lnxrobots/rcj-soccer-open/Hardware/3D/handle/handle-mount.stl

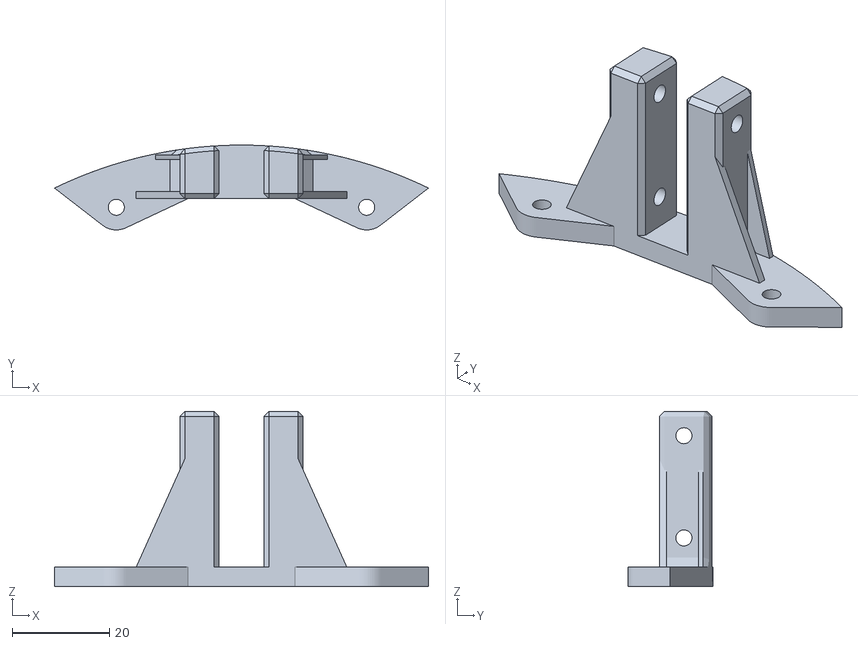
[picture p15: CAD file, 2023-08-07]
Hardware/3D/handle/handle-mount.stl
76.9 x 17.4 x 36.0
