lnxrobots/rcj-soccer-open/Hardware/3D/rack.stl

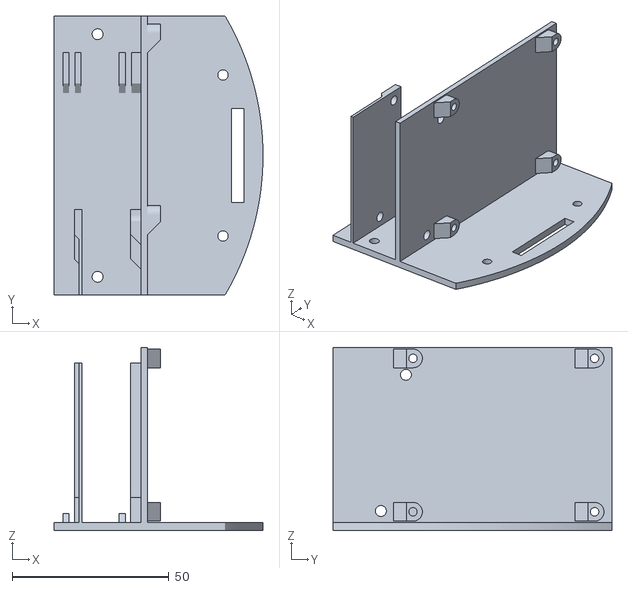
[picture p16: CAD file, 2023-08-07]
Hardware/3D/rack.stl
66.8 x 89.0 x 58.5
