lnxrobots/rcj-soccer-open/Hardware/3D/transport-container-adapter/adapter.stl

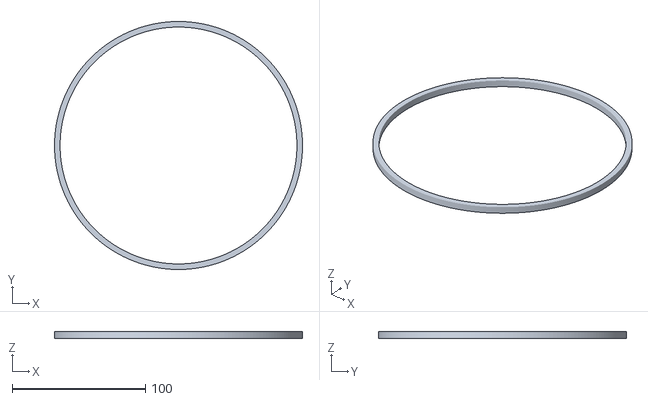
[picture p17: CAD file, 2023-08-07]
Hardware/3D/transport-container-adapter/adapter.stl
186.0 x 186.0 x 5.00
