lnxrobots/rcj-soccer-open/Hardware/3D/bumpers-35mm/bumper-side.stl

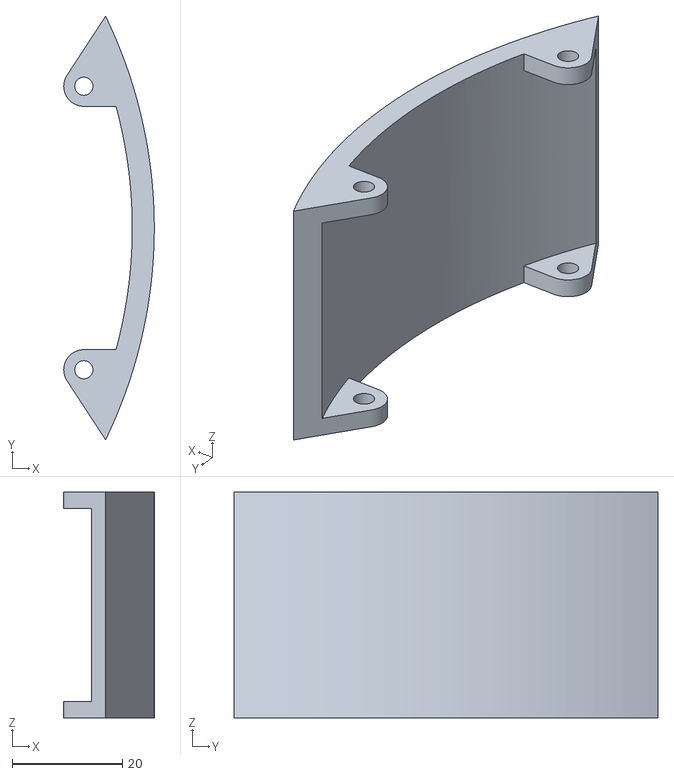
[picture p19: CAD file, 2023-08-07]
Hardware/3D/bumpers-35mm/bumper-side.stl
16.4 x 76.9 x 41.0
