lnxrobots/rcj-soccer-open/Hardware/3D/bumpers-40mm/bumper-40mm-front.stl

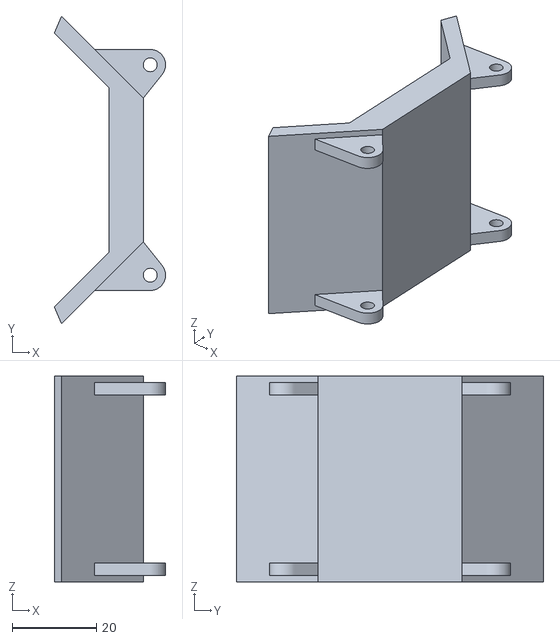
[picture p20: CAD file, 2023-08-07]
Hardware/3D/bumpers-40mm/bumper-40mm-front.stl
26.4 x 73.1 x 49.0
