lnxrobots/rcj-soccer-open/Hardware/3D/pcb-shaft.stl

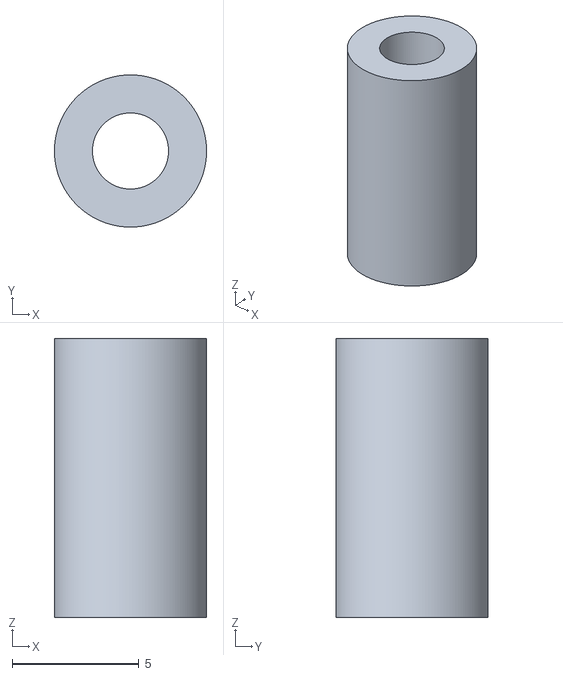
[picture p21: CAD file, 2023-08-07]
Hardware/3D/pcb-shaft.stl
6.00 x 6.00 x 11.0
