lnxrobots/rcj-soccer-open/Hardware/3D/battery-holders/battery-holder-small-right.stl

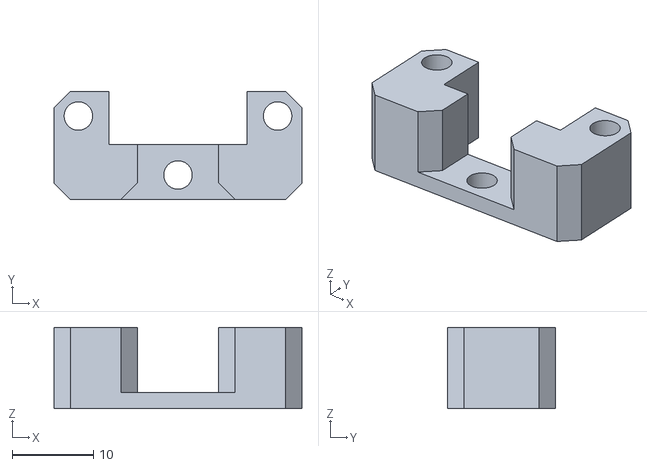
[picture p22: CAD file, 2023-08-07]
Hardware/3D/battery-holders/battery-holder-small-right.stl
30.5 x 13.2 x 10.0
