lnxrobots/rcj-soccer-open/Hardware/3D/omniwheel.3mf

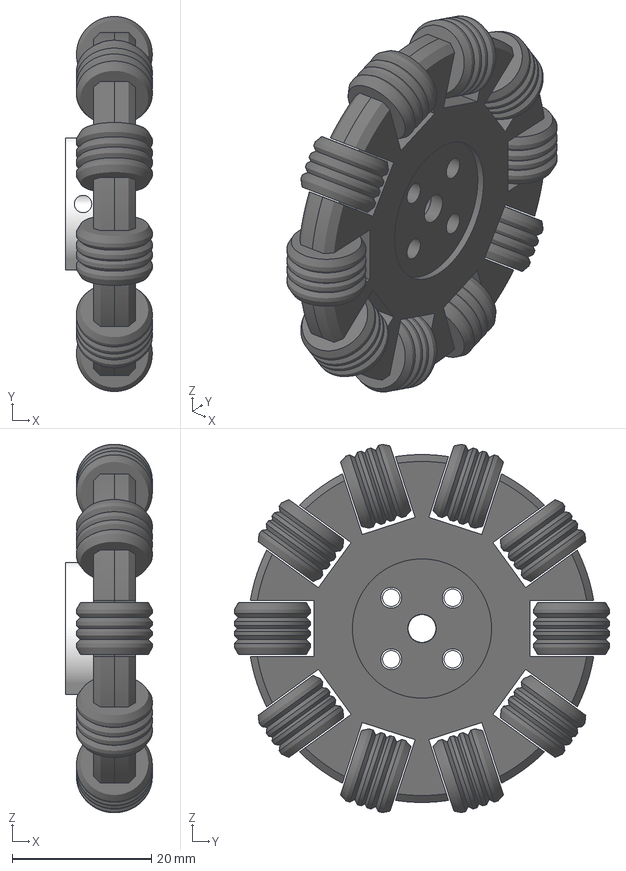
[picture p23: CAD file, 2023-08-07]
Hardware/3D/omniwheel.3mf
12.4 x 53.9 x 53.0 mm
Mounting Hub
Roller (1)
Roller (2)
Roller (3)
Roller (4)
Roller (5)
Roller (6)
Roller (7)
Roller (8)
Roller (9)
Roller
WheelBody (1)
WheelBody
