lnxrobots/rcj-soccer-open/Hardware/3D/rack-only-rpi.stl

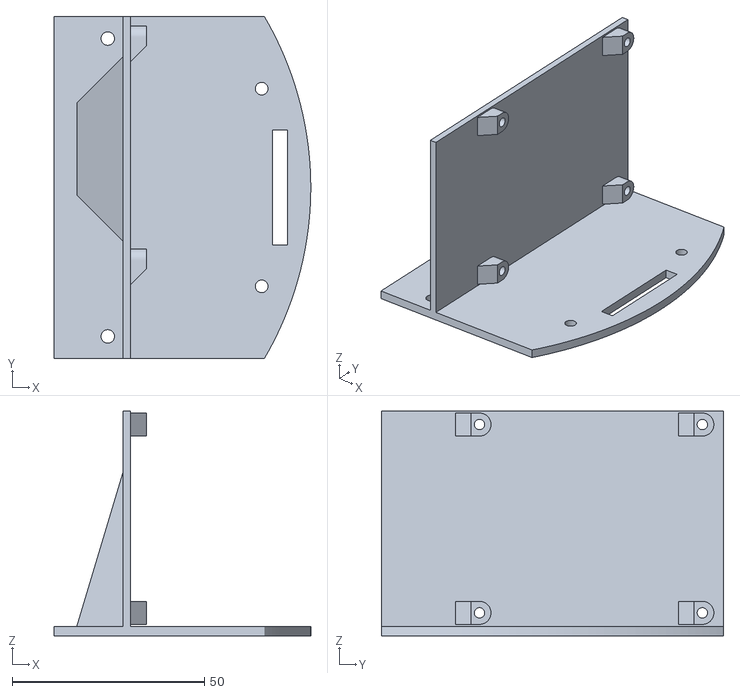
[picture p24: CAD file, 2023-08-07]
Hardware/3D/rack-only-rpi.stl
66.8 x 89.0 x 58.5
